filipandersson3/Gait-speed-lidar-system/Measurements/5_healthy_adults/gait_2025-05-12_15-40-24 normal 1/2025-05-12_15-37-18.csv

Time (s) | Distance (m)
0.02 | 1.03
0.04 | 1.04
0.07 | 1.07
0.08 | 1.07
0.11 | 1.08
0.12 | 1.09
0.15 | 1.12
0.16 | 1.13
0.19 | 1.16
0.2 | 1.18
0.23 | 1.22
0.24 | 1.24
0.27 | 1.27
0.28 | 1.29
0.3 | 1.32
0.32 | 1.35
0.35 | 1.38
0.36 | 1.39
0.38 | 1.42
0.4 | 1.44
0.43 | 1.48
0.44 | 1.5
0.46 | 1.53
0.48 | 1.58
0.51 | 1.6
0.52 | 1.63
0.54 | 1.64
0.56 | 1.65
0.58 | 1.68
0.6 | 1.71
0.62 | 1.73
0.64 | 1.73
0.67 | 1.76
0.68 | 1.78
0.7 | 1.82
0.72 | 1.84
0.74 | 1.86
0.76 | 1.89
0.78 | 1.9
0.8 | 1.93
0.82 | 1.95
0.84 | 1.98
0.86 | 2.0
0.88 | 2.02
0.9 | 2.05
0.92 | 2.09
0.95 | 2.13
0.96 | 2.14
0.99 | 2.17
1.0 | 2.2
1.02 | 2.23
1.04 | 2.25
1.06 | 2.28
1.08 | 2.32
1.11 | 2.34
1.12 | 2.38
1.14 | 2.43
1.16 | 2.46
1.18 | 2.48
1.2 | 2.5
1.22 | 2.53
1.24 | 2.55
1.26 | 2.57
1.28 | 2.58
1.3 | 2.61
1.32 | 2.64
1.35 | 2.66
1.36 | 2.67
1.38 | 2.7
1.4 | 2.72
1.42 | 2.75
1.44 | 2.77
1.46 | 2.79
1.48 | 2.81
1.5 | 2.83
1.52 | 2.87
1.54 | 2.88
1.56 | 2.92
1.58 | 2.94
1.6 | 2.96
1.62 | 3.0
1.64 | 3.02
1.66 | 3.06
1.68 | 3.07
1.7 | 3.09
1.72 | 3.13
1.74 | 3.15
1.76 | 3.16
1.79 | 3.2
1.8 | 3.21
1.82 | 3.22
1.84 | 3.25
1.87 | 3.29
1.88 | 3.3
1.9 | 3.32
1.92 | 3.34
1.94 | 3.35
1.96 | 3.38
1.99 | 3.4
2.0 | 3.41
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
