filipandersson3/Gait-speed-lidar-system/Measurements/5_healthy_adults/gait_2025-05-12_15-40-24 normal 1/2025-05-12_15-39-19.csv

Time (s) | Distance (m)
0.03 | 1.05
0.04 | 1.06
0.07 | 1.08
0.08 | 1.07
0.1 | 1.09
0.12 | 1.11
0.14 | 1.13
0.16 | 1.15
0.19 | 1.17
0.2 | 1.2
0.23 | 1.22
0.24 | 1.23
0.26 | 1.25
0.28 | 1.27
0.3 | 1.29
0.32 | 1.32
0.34 | 1.35
0.36 | 1.37
0.38 | 1.38
0.4 | 1.41
0.42 | 1.44
0.44 | 1.47
0.46 | 1.49
0.48 | 1.52
0.5 | 1.56
0.52 | 1.6
0.54 | 1.62
0.56 | 1.64
0.58 | 1.67
0.6 | 1.69
0.62 | 1.72
0.64 | 1.74
0.66 | 1.75
0.68 | 1.78
0.7 | 1.82
0.72 | 1.84
0.74 | 1.86
0.76 | 1.88
0.79 | 1.89
0.8 | 1.91
0.82 | 1.93
0.84 | 1.96
0.86 | 1.97
0.88 | 2.0
0.91 | 2.02
0.92 | 2.03
0.94 | 2.06
0.96 | 2.1
0.98 | 2.13
1.0 | 2.14
1.02 | 2.17
1.04 | 2.21
1.06 | 2.24
1.08 | 2.26
1.1 | 2.28
1.12 | 2.32
1.14 | 2.36
1.16 | 2.38
1.18 | 2.41
1.2 | 2.44
1.22 | 2.46
1.24 | 2.48
1.26 | 2.52
1.28 | 2.53
1.3 | 2.54
1.32 | 2.57
1.35 | 2.59
1.36 | 2.6
1.38 | 2.63
1.4 | 2.66
1.42 | 2.68
1.44 | 2.69
1.46 | 2.73
1.48 | 2.76
1.5 | 2.78
1.52 | 2.8
1.54 | 2.83
1.56 | 2.84
1.59 | 2.86
1.6 | 2.9
1.62 | 2.92
1.64 | 2.95
1.66 | 2.96
1.68 | 3.0
1.71 | 3.04
1.72 | 3.06
1.74 | 3.08
1.76 | 3.11
1.78 | 3.13
1.8 | 3.16
1.82 | 3.17
1.84 | 3.19
1.86 | 3.24
1.88 | 3.27
1.9 | 3.29
1.92 | 3.29
1.94 | 3.32
1.96 | 3.35
1.98 | 3.36
2.0 | 3.39
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
