filipandersson3/Gait-speed-lidar-system/Measurements/5_healthy_adults/gait_2025-05-12_15-40-24 normal 1/2025-05-12_15-40-02.csv

Time (s) | Distance (m)
0.02 | 1.03
0.05 | 1.04
0.06 | 1.06
0.08 | 1.08
0.1 | 1.09
0.12 | 1.1
0.14 | 1.12
0.16 | 1.14
0.18 | 1.16
0.2 | 1.19
0.22 | 1.2
0.24 | 1.23
0.26 | 1.24
0.28 | 1.27
0.3 | 1.29
0.32 | 1.32
0.34 | 1.34
0.36 | 1.35
0.38 | 1.38
0.4 | 1.39
0.42 | 1.41
0.44 | 1.44
0.46 | 1.44
0.49 | 1.49
0.5 | 1.51
0.53 | 1.53
0.54 | 1.55
0.56 | 1.58
0.58 | 1.6
0.61 | 1.62
0.62 | 1.64
0.64 | 1.67
0.66 | 1.71
0.68 | 1.74
0.7 | 1.76
0.72 | 1.79
0.74 | 1.83
0.76 | 1.85
0.78 | 1.86
0.8 | 1.89
0.82 | 1.9
0.84 | 1.94
0.86 | 1.96
0.88 | 1.97
0.9 | 2.0
0.92 | 2.01
0.94 | 2.04
0.97 | 2.06
0.98 | 2.11
1.01 | 2.13
1.02 | 2.14
1.04 | 2.17
1.06 | 2.19
1.08 | 2.2
1.1 | 2.24
1.12 | 2.25
1.14 | 2.27
1.16 | 2.31
1.18 | 2.33
1.2 | 2.37
1.22 | 2.4
1.24 | 2.43
1.26 | 2.45
1.28 | 2.49
1.3 | 2.51
1.32 | 2.54
1.34 | 2.57
1.36 | 2.59
1.38 | 2.63
1.4 | 2.64
1.42 | 2.67
1.44 | 2.69
1.46 | 2.73
1.48 | 2.74
1.5 | 2.76
1.52 | 2.78
1.54 | 2.8
1.57 | 2.81
1.58 | 2.82
1.6 | 2.84
1.62 | 2.86
1.64 | 2.89
1.66 | 2.92
1.68 | 2.94
1.7 | 2.95
1.72 | 2.97
1.74 | 3.01
1.76 | 3.02
1.78 | 3.05
1.8 | 3.07
1.82 | 3.1
1.84 | 3.12
1.86 | 3.13
1.88 | 3.17
1.9 | 3.2
1.92 | 3.22
1.94 | 3.26
1.96 | 3.29
1.98 | 3.3
2.0 | 3.34
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
