filipandersson3/Gait-speed-lidar-system/Measurements/5_healthy_adults/gait_2025-05-12_16-20-50 fast 1/2025-05-12_16-18-35.csv

Time (s) | Distance (m)
0.02 | 1.06
0.05 | 1.11
0.06 | 1.12
0.08 | 1.13
0.1 | 1.15
0.12 | 1.19
0.14 | 1.23
0.16 | 1.27
0.18 | 1.3
0.2 | 1.32
0.22 | 1.35
0.24 | 1.37
0.26 | 1.41
0.28 | 1.46
0.3 | 1.48
0.32 | 1.55
0.34 | 1.55
0.37 | 1.6
0.38 | 1.64
0.4 | 1.67
0.42 | 1.7
0.45 | 1.76
0.46 | 1.78
0.48 | 1.83
0.5 | 1.87
0.52 | 1.91
0.54 | 1.95
0.57 | 2.0
0.58 | 2.02
0.6 | 2.05
0.62 | 2.11
0.65 | 2.15
0.66 | 2.17
0.68 | 2.2
0.7 | 2.23
0.72 | 2.27
0.74 | 2.3
0.76 | 2.35
0.78 | 2.38
0.81 | 2.44
0.82 | 2.46
0.85 | 2.49
0.86 | 2.52
0.88 | 2.55
0.9 | 2.58
0.92 | 2.62
0.94 | 2.68
0.97 | 2.72
0.98 | 2.75
1.01 | 2.81
1.02 | 2.83
1.04 | 2.88
1.06 | 2.89
1.08 | 2.93
1.1 | 2.96
1.13 | 3.01
1.14 | 3.04
1.16 | 3.07
1.18 | 3.09
1.2 | 3.13
1.22 | 3.17
1.24 | 3.2
1.26 | 3.23
1.28 | 3.28
1.3 | 3.31
1.32 | 3.34
1.34 | 3.38
1.36 | 3.4
1.38 | 3.42
1.41 | 3.45
1.42 | 3.49
1.44 | 3.54
1.46 | 3.58
1.48 | 3.62
1.5 | 3.67
1.52 | 3.71
1.54 | 3.75
1.56 | 3.79
1.58 | 3.82
1.6 | 3.86
1.62 | 3.89
1.65 | 3.94
1.66 | 3.97
1.68 | 4.0
1.7 | 4.04
1.72 | 4.07
1.74 | 4.1
1.76 | 4.15
1.78 | 4.17
1.8 | 4.19
1.82 | 4.24
1.84 | 4.26
1.86 | 4.3
1.89 | 4.33
1.9 | 4.36
1.93 | 4.41
1.94 | 4.45
1.96 | 4.48
1.98 | 4.52
2.0 | 4.56
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
